tomcatzh/wallboard-rail-hooks/wiki/entities/mounting-rail.md

---
title: "Mounting Rail (wall panel insert strip)"
type: entity
status: active
sources:
  - raw/rail/hook-full-view.jpg
  - https://www.chinayoubang.com/productfamily/detail/195.html
updated: 2026-07-10
---

# Mounting Rail（墙板挂条）

## Summary（摘要）

EN: A champagne-gold aluminum strip inset horizontally into a seam of the white leather-textured wall paneling. Its front face carries fine horizontal ribs; along its top edge runs a continuous slot behind a front lip, into which claw-type hooks drop. It is existing infrastructure — the hook must adapt to it, not vice versa.
ZH: 一条水平嵌在白色皮纹墙板接缝中的香槟金色铝条。正面有细密水平棱纹；顶缘沿全长有一条位于前唇后方的连续槽，爪式挂钩由此扣入。它是既有设施 —— 是挂钩去适配它，而不是反过来。

## Product Identity（产品身份）

EN: The rail is the "parallel function strip" of Youbang wallboard's (友邦墙板) GuaGuaQiang (挂挂墙) Parallel series (平行系列) — official page: <https://www.chinayoubang.com/productfamily/detail/195.html>. Published spec: strip W×H×D = 3000×48×11 mm; material "native 6-series aluminum", anodized — consistent with the 6063-class assumption used in the strength review. Wallboard is Youbang "5K wood". Colors include 古铜黄 (antique bronze), matching our photos. The page does NOT publish slot/lip dimensions — the hook-side measurements in [rail-hook](rail-hook.md) remain the fit authority. Cite this section when publishing the project.
ZH: 挂条是友邦墙板「挂挂墙 · 平行系列」的"平行功能条" —— 官方页面：<https://www.chinayoubang.com/productfamily/detail/195.html>。公开规格：功能条 W×H×D = 3000×48×11 mm；材质"原生六系铝"、阳极氧化 —— 与强度审查中 6063 系的假设一致。墙板为友邦 5K 木。颜色含古铜黄，与我们的照片相符。页面**未**公布槽口/唇的尺寸 —— 配合仍以 [rail-hook](rail-hook.md) 中挂钩侧的实测为准。公开项目时引用本节说明来源。

## Observed Features（观察到的特征）

- EN: Ribbed front face; rib pitch well under 1 mm, visually matching the hook's serrated patch.
  ZH: 正面棱纹面；棱距远小于 1 mm，与挂钩的锯齿区在视觉上匹配。
- EN: A continuous dark slot line along the top edge where the hook's claw enters.
  ZH: 顶缘有一条连续深色缝线，挂钩的爪由此进入。
- EN: A smooth gold band above the ribbed strip (upper flange of the same profile, or a separate trim — undetermined).
  ZH: 棱纹条上方有一条光滑金色带（同一型材的上翻边，或独立饰条 —— 未确定）。
- EN: A 2026-07-10 caliper probe showed the earlier 1.6 mm lower-wallboard setback estimate was conservative, leading to otherwise-identical 2.0/2.5 mm half-width probes. The user selected 2.0 mm and promoted it into the production library. Treat 2.0 mm as the accepted accessory reach, not a direct measurement of the rail profile (the WeChat image remains in chat, not under `raw/`).
  ZH: 2026-07-10 的游标卡尺探测表明，此前下方墙板后退量 1.6 mm 的估计偏保守，因此制作了其余几何相同的 2.0/2.5 mm 半宽探针。用户最终选择 2.0 mm 并将其并入正式库。应把 2.0 mm 视为配件定案凸高，而不是轨道截面的直接实测值（WeChat 图片仍在聊天中，未存入 `raw/`）。
- EN: Implied clearances: the strip's bottom edge lies above the hook's wall pad (pad top ≈7–8.5 below the slot ceiling), and the panel above the strip is exposed at cap height (≈10.7–11.2 above the ceiling).
  ZH: 反推的空间关系：挂条下缘在挂钩抵墙凸台之上（凸台上缘约在槽顶下方 7–8.5）；挂条上方在顶帽高度（槽顶上方约 10.7–11.2）处露出墙板面。

## Interface Constraints Implied by the Hook（由挂钩尺寸反推的接口约束）

EN: The rail was not measured directly; these bounds follow from the hook's annotated dimensions (see [rail-hook](rail-hook.md)):
ZH: 挂条本身没有直接测量；以下边界由挂钩的标注尺寸反推（见 [rail-hook](rail-hook.md)）：

- EN: Top lip thickness < 2.75 mm (it must fit inside the claw slot).
  ZH: 上唇厚度 < 2.75 mm（要放进爪槽）。
- EN: Cavity behind the lip: ≥ ~2.4 mm front-to-back and ≥ ~6 mm deep (it must accept the claw finger).
  ZH: 上唇后方腔体：前后向 ≥ 约 2.4 mm、深度 ≥ 约 6 mm（要容纳爪指）。

## Superseded / Revised（已废弃 / 已修订）

- EN: "The strip front is uniformly ≈0.8 mm proud of the wall panel" — this 2026-07-09 inference came from the original hook's 0.8 mm top cap and back pad, not from a direct rail-to-panel measurement. The 2026-07-10 lower-panel observation is ≈1.6 mm, so upper and lower panel relationships must no longer be assumed identical.
  ZH: “挂条正面统一比墙板面凸出约 0.8 mm” —— 这个 2026-07-09 推论来自原钩顶部小帽与背面凸台均为 0.8 mm，并非轨道到墙板的直接测量。2026-07-10 对下方墙板的观察约为 1.6 mm，因此不能再假定轨道上下两侧的墙板空间关系完全相同。

## Open Questions（开放问题）

- EN: Exact rail profile (extrusion cross-section) and strip height are unknown — not required for replicating the hook, since the fit is already encoded in the hook's own dimensions.
  ZH: 挂条的精确型材截面与条高未知 —— 复刻挂钩并不需要它们，因为配合关系已经编码在挂钩自身尺寸里。
- EN: Whether the rail also has a bottom lip, and the exact lower-panel setback. The accessory geometry no longer depends on resolving these immediately because 2.0 mm has been selected, but a direct rail cross-section measurement would improve future variants.
  ZH: 挂条是否还有下唇，以及下方墙板的精确后退量。由于 2.0 mm 配件几何已经定案，当前不再依赖立即解决这些问题；但直接测得轨道截面仍可改进未来变体。
- EN: Interior headroom above the slot opening: my photo estimate put the opening at ≈4 mm, but the user (who has the rail in hand) judged a much larger reinforcement feasible — the hook's arc gusset now rises 7.2 above the ceiling inside the rail. Next test fit settles it: if the arc fouls the rail's interior or blocks tilt-in insertion, reduce `arm_gusset_r`.
  ZH: 槽口上方的内部净空：照片估计开口约 4 mm，但（手上有实物的）用户判断可以放大得多 —— 挂钩的圆弧加强现已在挂条内部升到槽顶上方 7.2。下一次试装可定案：若圆弧顶到挂条内部或妨碍斜插入，就调小 `arm_gusset_r`。
