tomcatzh/wallboard-rail-hooks/wiki/entities/rail-hook.md

---
title: "Rail Hook (replication target)"
type: entity
status: active
sources:
  - raw/rail/hook-mount-dimensions.jpg
  - raw/rail/hook-installed-on-rail.jpg
  - raw/rail/hook-full-view.jpg
updated: 2026-07-09
---

# Rail Hook（墙板轨道挂钩）

## Summary（摘要）

EN: A small J-shaped hanging hook in champagne-gold metal that clips tool-free onto a slatwall-style metal rail inset in wall paneling. It is the replication target of this project. The top "mounting claw" is the precision interface that engages the rail — its dimensions are annotated in the source photos and must be reproduced exactly. Per the user (2026-07-09), the overall height and the protruding J-hook are variable parts that may be adapted freely. See [hook-replication-requirements](../topics/hook-replication-requirements.md).
ZH: 一个香槟金色金属的小型 J 形挂钩，无需工具即可扣到嵌在墙板里的 slatwall（槽板）式金属挂条上。它是本项目的复刻对象。顶部的 mounting claw（安装爪）是与挂条配合的精密接口 —— 其尺寸在来源照片中有标注，必须精确复刻。用户已明确（2026-07-09）：总高与外伸的 J 钩是可变部分，可以自由调整。见 [hook-replication-requirements](../topics/hook-replication-requirements.md)。

## Construction（构造）

EN: The hook is almost certainly a slice cut from a long aluminum extrusion: the entire shape is a constant 2D profile swept along the hook's width, the front serration ridges run along that width axis, and the cut side faces show uniform machining marks. `hook-mount-dimensions.jpg` is literally the extrusion cross-section seen end-on. Consequence for replication: getting the 2D profile right (especially in the claw region) captures the entire fit; width is a separate single number.
ZH: 这个挂钩几乎可以肯定是从一根长 aluminum extrusion（铝挤出型材）上切下的一段：整个形状是一个恒定的 2D profile（二维截面）沿挂钩宽度方向扫掠而成，正面锯齿棱沿宽度方向延伸，切割侧面有均匀加工纹。`hook-mount-dimensions.jpg` 就是沿挤出轴方向看到的端面截面。对复刻的意义：把 2D 截面（尤其爪部区域）做准就抓住了全部配合关系；宽度只是另外一个独立数字。

EN: Descriptive coordinate convention for later reference (not a plan): the profile plane is the vertical plane perpendicular to the rail; +X points away from the wall (room side), +Y points up; the extrusion/width direction runs along the rail.
ZH: 为后续引用约定的描述性坐标（不是计划）：profile 平面为垂直于挂条的竖直平面；+X 指向远离墙面（房间一侧），+Y 向上；挤出/宽度方向沿挂条延伸。

## Profile, top to bottom（截面自上而下）

- EN: **Top cap** — a 0.5 mm tall cap at the plate top, thickened to 3.0 mm total by protruding 0.8 mm toward the wall (D15). It bears on the wall panel above the rail and stabilizes the hook against over-rotation. (The earlier "slanted top edge" reading is superseded — see below.)
  ZH: **顶部小帽** —— 主板顶部高 0.5 mm 的小帽，向墙面凸出 0.8 mm、总厚 3.0 mm（D15）。抵在挂条上方的墙板面上，防止挂钩过度转动、辅助受力。（早先“顶边斜切”的解读已废弃 —— 见下文。）
- EN: **Front face, serrated patch** — fine horizontal ridges (pitch well under 1 mm) covering roughly the top ~15 mm of the front face. When installed this patch overlaps the rail's ribbed face and visually blends the hook into the rail. The ridges face the room, so they are cosmetic, not a grip surface.
  ZH: **正面锯齿区** —— 细密水平棱纹（间距远小于 1 mm），覆盖正面顶部约 15 mm。安装后这块区域正好叠在挂条的棱纹面上，使挂钩在视觉上融入挂条。棱纹朝向房间一侧，是装饰性的，不是摩擦面。
- EN: **Mounting claw (back side)** — below the plate top, a bridge arm projects rearward (toward the wall) from the plate, then turns down into a rear finger, forming a downward-opening claw. The gap between finger and plate is the slot that swallows the rail's top lip. Front-to-back order when installed: plate (room side) → slot (rail lip sits here) → finger (wall side). Outer corners are slightly rounded; the finger tip is a slanted point (user-confirmed 2026-07-09): lowest at the outer/wall face, its bottom rising ≈1.5 mm toward the inner face — an insertion ramp that rides over the lip during tilt-in.
  ZH: **安装爪（背面）** —— 在主板顶部下方，一条 bridge arm（顶桥）从主板向后（朝墙）伸出，再向下折成后爪指，构成开口朝下的爪。爪指与主板之间的缝隙就是吞住挂条上唇的槽。安装后从前到后的顺序：主板（房间侧）→ 槽（挂条上唇在此）→ 爪指（墙侧）。外侧转角略有圆角；爪指末端是斜尖（用户 2026-07-09 确认）：最低点在外侧/墙侧，底面向内侧斜升约 1.5 mm —— 翻入轨道时骑过上唇的导向斜面。
- EN: **Back wall pad** — below the rail zone the back face bulges 0.8 mm TOWARD the wall (total 3.0 mm thick, D13) and runs down into the J. It braces against the wall panel and carries the horizontal reaction H — the original's built-in answer to the tipping moment. Together with the cap it implies the panel surface sits ≈0.8 mm behind the rail face.
  ZH: **背面抵墙凸台** —— 挂条区以下，背面向墙面方向凸出 0.8 mm（总厚 3.0 mm，D13），向下延伸并入 J 钩。它抵住墙板、承担水平反力 H —— 是原件对倾覆力矩的自带解决方案。结合小帽可推出：墙板面比挂条正面靠后约 0.8 mm。
- EN: **J-hook** — the shank sweeps into a J curve opening up-and-away from the wall; the section appears to thicken gradually toward the tip end of the curve. A small V-notch is visible on the inner face right at the tip in the bare-hook photo (possibly a retention nib for loops/strings, possibly a cutting artifact — unconfirmed).
  ZH: **J 钩** —— 杆身向下弯成 J 形曲线，开口朝上并远离墙面；截面似乎向钩尖一端逐渐加厚。裸钩照片中钩尖内侧面可见一个小 V 形缺口（可能是防止挂绳滑落的小卡口，也可能是切割痕迹 —— 未确认）。

## Dimensions（尺寸）

EN: D1–D3 are the three annotations written on `hook-mount-dimensions.jpg` and are the authoritative numbers. D4 is derived from them. All others are photo-scale estimates: calibrated at ≈23 px/mm on the bare-hook profile photo using D1 as scale; the claw's total depth then measures ≈7.4 mm, matching D3 = 7.35 mm, which validates the scale.
ZH: D1–D3 是写在 `hook-mount-dimensions.jpg` 上的三个标注，是权威数字。D4 由它们推导。其余均为照片比例估计：以 D1 为尺度在裸钩侧面照上标定 ≈23 px/mm；用该尺度量得爪部总深 ≈7.4 mm，与 D3 = 7.35 mm 吻合，验证了该比例。

| # | Feature（部位） | Value | Basis（依据） | Confidence |
|---|---|---|---|---|
| D1 | Rear finger thickness, wall-normal（后爪指厚度，垂直墙面方向） | 2.40 mm | annotated（照片标注） | high |
| D2 | Claw slot gap, finger↔plate（爪槽宽，容纳挂条上唇） | 2.75 mm | annotated | high — user-confirmed（用户已确认） |
| D3 | Mounting-head total depth, serrated front face→finger back face（安装头总深：锯齿正面→爪指背面） | 7.35 mm | annotated | high |
| D4 | Plate thickness at claw level（主板在爪部高度的厚度） | ≈2.20 mm | derived: D3−D2−D1 | medium |
| D5 | Bridge-arm vertical thickness（顶桥竖直厚度） | ≈2.2 mm | photo-scale estimate | low — measure |
| D6 | Finger vertical length / slot depth（爪指竖直长度 / 槽深） | 6.75 mm (claw total arm+finger = 9.0 measured) | user caliper 2026-07-09 | high — measured（已实测） |
| D7 | Plate extension above bridge-arm top（主板高出顶桥的高度） | 8.8 mm (build 9.0) | user caliper 2026-07-09 | high — measured（已实测） |
| D8 | Serrated patch height（正面锯齿区高度） | ≈15 mm | photo-scale estimate | low |
| D9 | Overall hook height（挂钩总高） | ≈40 mm | photo-scale estimate | variable by design（设计可变） |
| D10 | Hook width along rail（挂钩宽度，沿挂条/挤出方向） | 11.9 mm | user caliper 2026-07-09 | high — measured; still design-variable（已实测；仍可自由改） |
| D11 | J-hook inner radius（J 钩内半径） | ≈5–6 mm | photo-scale estimate | variable by design（设计可变） |
| D12 | J-hook wall thickness（J 钩壁厚） | ≈2.8–4 mm (thickens toward tip end) | photo-scale estimate | variable by design（设计可变） |
| D13 | Back wall pad（背面抵墙凸台） | total 3.0 thick = 0.8 wall-ward of plate back; top edge ≈7–8.5 below ceiling, runs into the J（总厚 3.0 = 向墙凸 0.8；上缘在槽顶下方≈7–8.5，向下并入 J） | user statement + photos 2026-07-09 | high (thickness) / low (top edge) |
| D14 | Serration pitch（锯齿间距） | ≈0.5–0.8 mm | photo-scale estimate | very low |
| D15 | Top cap（顶部小帽） | 0.5 tall × 3.0 total thick, 0.8 wall-ward（高 0.5 × 总厚 3.0，向墙凸 0.8） | user caliper 2026-07-09 | high — measured |
| D16 | Finger tip taper（爪尖斜面高度） | ≈1.5, point at the outer face（尖在外侧/墙侧） | photo estimate; direction user-confirmed | medium |

EN: Basis legend — annotated = written on the photo; derived = computed from annotated values; estimate = pixel-scale reading. Everything at low/very-low confidence must be caliper-measured before modeling; see the wishlist in [hook-replication-requirements](../topics/hook-replication-requirements.md).
ZH: 依据说明 —— annotated = 照片上的标注；derived = 由标注值推导；estimate = 像素比例读数。所有 low / very low 置信度的尺寸在建模前必须用卡尺实测，见 [hook-replication-requirements](../topics/hook-replication-requirements.md) 的待测清单。

## Annotation Interpretation（标注解读）

EN: The three annotations are tick-mark pairs drawn on the cross-section photo; the mapping below was determined from tick positions relative to the profile features.
ZH: 三个标注是画在截面照片上的成对刻度线；下面的对应关系由刻度线相对截面特征的位置判定。

- EN: **2.4 mm** — the tick pair flanks the rear finger, label below it → rear finger thickness (D1). High confidence.
  ZH: **2.4 mm** —— 刻度线夹住后爪指，标签在其下方 → 后爪指厚度（D1）。高置信度。
- EN: **2.75 mm** — the tick pair is drawn above the bridge arm but horizontally aligns with the slot walls (finger inner face / plate back face) → slot gap (D2). High-medium confidence.
  ZH: **2.75 mm** —— 刻度线画在顶桥上方，但水平位置对齐槽的两壁（爪指内侧面 / 主板背面）→ 槽宽（D2）。中高置信度。
- EN: **7.35 mm** — the tick pair flanks the whole head, from finger back face to plate front (serrated) face → total mounting-head depth (D3). High confidence.
  ZH: **7.35 mm** —— 刻度线夹住整个安装头，从爪指背面到主板正面（锯齿面）→ 安装头总深（D3）。高置信度。
- EN: Caveat: in both photos the slot *looks* narrower than the finger, yet the annotations say slot 2.75 > finger 2.4. Shadow inside the slot plus perspective (the finger sits closer to the camera) explains this, and the numbers are self-consistent (D4 ≈ 2.2 mm plate ≈ bridge-arm thickness ≈ a uniform extrusion wall), but user confirmation is welcome.
  ZH: 注意：两张照片里槽*看起来*都比爪指窄，而标注却是槽 2.75 > 爪指 2.4。槽内阴影加上透视（爪指更靠近相机）可以解释，且数字自洽（D4 ≈ 2.2 mm 主板厚 ≈ 顶桥厚 ≈ 均匀挤出壁厚），但欢迎用户确认。
- EN: Confirmed: on 2026-07-09 the user reviewed side-view sketches drawn from this interpretation (including the claw-over-lip mounting model) and confirmed they are correct. The mapping above is settled.
  ZH: 已确认：2026-07-09 用户审阅了按此解读绘制的侧视图草图（含爪扣上唇的安装模型），确认无误。上述对应关系定案。

## Mounting Interaction（安装配合）

EN: To install, the claw drops over the rail's top edge from the front: the rail's top lip enters the 2.75 mm slot, the 2.4 mm finger hides behind the lip inside the rail cavity, and the plate's smooth back face rests on the lip's front face. Load on the J-hook torques the hook so the lower shank presses toward the wall — self-locking, no fasteners. The serrated patch overlaps the rail's ribbed face for visual continuity. See [mounting-rail](mounting-rail.md).
ZH: 安装时，安装爪从前方扣到挂条顶缘上：挂条上唇进入 2.75 mm 的槽，2.4 mm 的爪指藏进上唇后方的挂条腔体，主板光滑的背面贴在上唇正面。J 钩受载产生的力矩使下段杆身压向墙面 —— 自锁，无需紧固件。锯齿区叠在挂条棱纹面上，保持视觉连续。见 [mounting-rail](mounting-rail.md)。

## Evidence（证据）

- EN: `raw/rail/hook-mount-dimensions.jpg` — end-on cross-section of the mounting head with the three dimension annotations; serration teeth visible on the front edge.
  ZH: `raw/rail/hook-mount-dimensions.jpg` —— 安装头的端面截面，带三个尺寸标注；正面边缘可见锯齿。
- EN: `raw/rail/hook-installed-on-rail.jpg` — despite its filename, shows the bare hook's full side profile on a plain background; source of the photo-scale estimates.
  ZH: `raw/rail/hook-installed-on-rail.jpg` —— 与文件名相反，实际是纯色背景上裸钩的完整侧面轮廓；照片比例估计的来源。
- EN: `raw/rail/hook-full-view.jpg` — despite its filename, shows the hook installed on the gold rail in the wall paneling; source for the mounting interaction and rib blending.
  ZH: `raw/rail/hook-full-view.jpg` —— 与文件名相反，实际是挂钩安装在墙板金色挂条上的照片；安装配合与棱纹融合观察的来源。
- EN: 2026-07-09 chat photos — a v3 print seats correctly on the real rail (claw over lip, cap and pad engaged): the mount interface is physically validated.
  ZH: 2026-07-09 对话照片 —— v3 打印件在真实挂条上正确就位（爪扣唇、帽与凸台到位）：安装接口已实物验证。

## Superseded（已废弃的解读）

- EN: "Slanted top edge (front high, sloping to the wall side)" — superseded 2026-07-09 by the user's close-up photos and calipers: the feature is the 0.5×3.0 top cap (D15).
  ZH: “顶边斜切（前高后低）” —— 2026-07-09 被用户微距照片与卡尺推翻：该特征实为 0.5×3.0 的顶部小帽（D15）。
- EN: "Back-face step toward the room (shank thinner below)" — superseded: the feature is the 0.8 mm wall-ward pad (D13). hook.scad v1/v2 modeled the wrong direction; corrected in v3.
  ZH: “背面向房间收薄的台阶” —— 已废弃：该特征实为向墙凸 0.8 mm 的抵墙凸台（D13）。hook.scad v1/v2 方向建反；v3 已纠正。
- EN: "D7 ≈ 6.5–7 mm" — superseded by caliper 8.8 mm. Root cause: photo verticals are foreshortened ≈25% (perspective); remaining photo-derived vertical estimates (D5, D6, D8, D9) should be read ≈25% larger until measured.
  ZH: “D7 ≈ 6.5–7 mm” —— 被卡尺实测 8.8 mm 取代。根因：照片竖直方向被透视压缩约 25%；其余照片竖直估计（D5、D6、D8、D9）在实测前都应按放大约 25% 理解。

## Open Questions（开放问题）

- EN: D6 settled: claw total (arm+finger) caliper-measured ≈9.0 → finger 6.75 with the arm at 2.2. D5 (arm) itself is still a photo estimate, but the user's 6.75 split implies arm ≈2.2–2.25, so the earlier ≈2.7 suspicion is retracted; the authoritative number is the 9.0 total.
  ZH: D6 定案：爪部总高（顶桥+爪指）卡尺实测 ≈9.0 → 顶桥按 2.2 时爪指为 6.75。D5（顶桥）本身仍是照片估计，但用户给出的 6.75 拆分意味着顶桥 ≈2.2–2.25，此前 ≈2.7 的猜测撤回；权威数字是总高 9.0。
- EN: Wall-pad top edge height (D13) — must clear the rail strip's bottom edge; the model defaults to 8.0 below the ceiling. Confirm at test fit.
  ZH: 抵墙凸台上缘高度（D13）—— 必须让开挂条下缘；模型默认取槽顶下方 8.0。试装确认。
- EN: Tip V-notch and serration details (D8, D14) sit in the variable body — replicate loosely or drop.
  ZH: 钩尖 V 缺口与锯齿细节（D8、D14）属于可变部分 —— 可宽松复刻或省略。
