tomcatzh/wallboard-rail-hooks/raw/accessories/frame-ribba22/existing-flat-hook.jpg

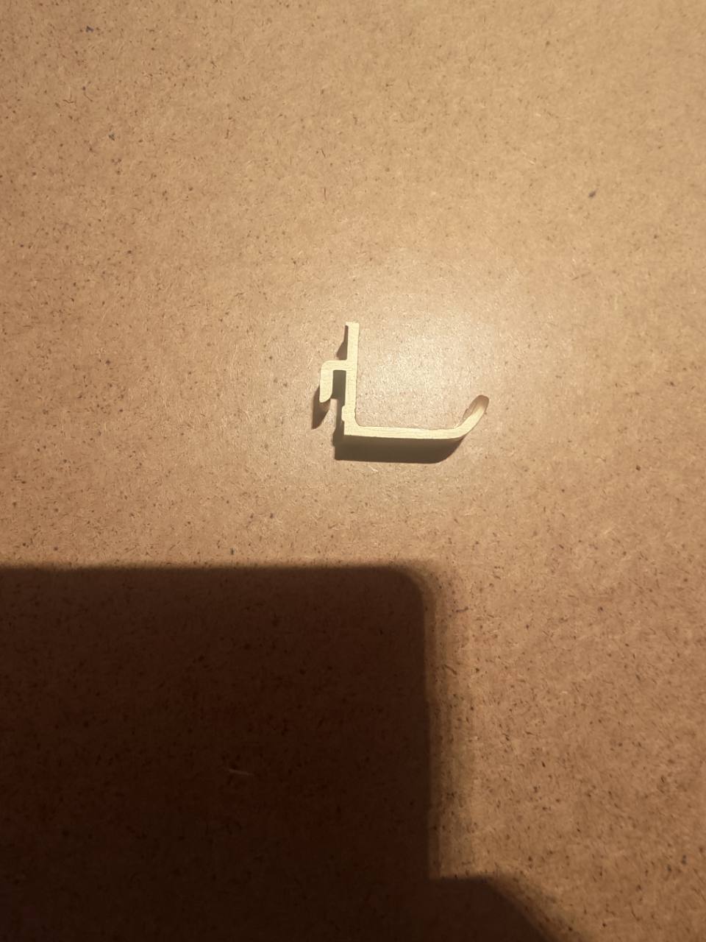
raw/accessories/frame-ribba22/existing-flat-hook.jpg
