tomcatzh/wallboard-rail-hooks/raw/accessories/frame-ribba22/recessed-back.jpg

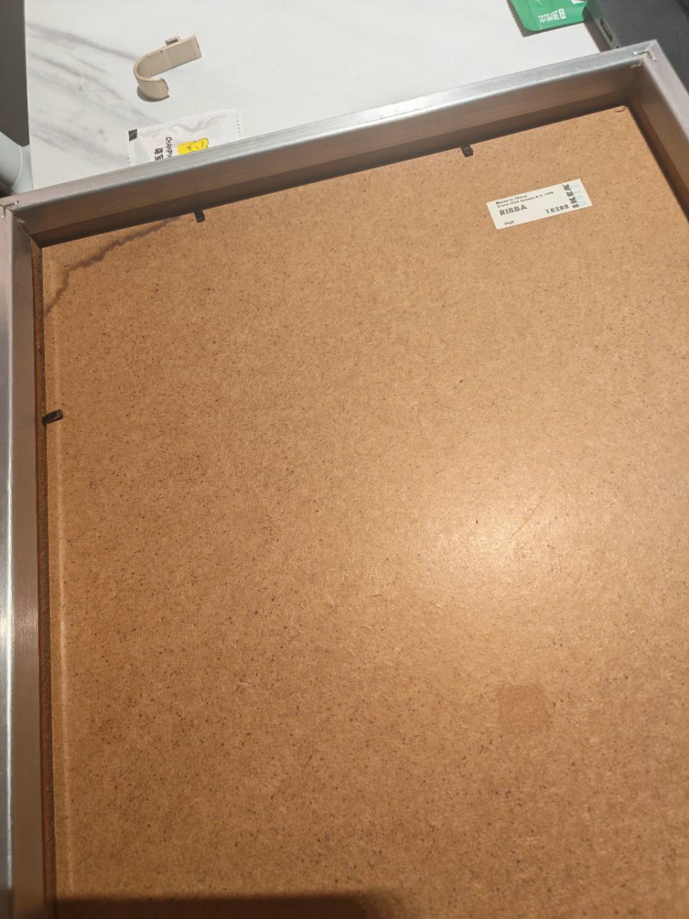
raw/accessories/frame-ribba22/recessed-back.jpg
