tomcatzh/wallboard-rail-hooks/raw/accessories/frame-ribba22/ribba-label.jpg

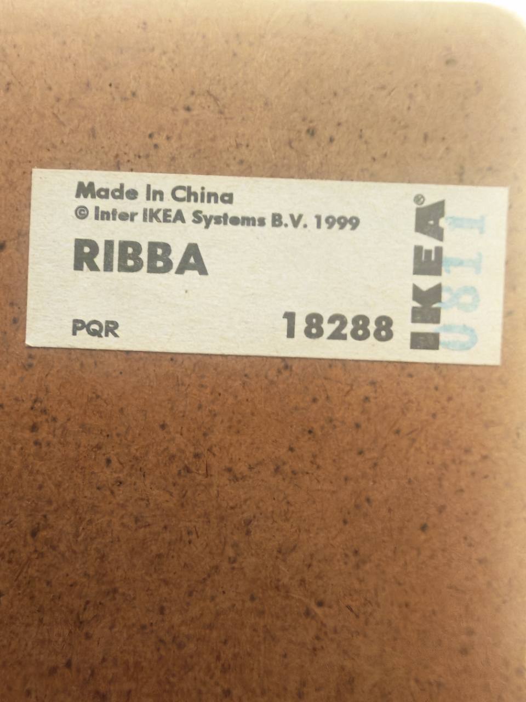
raw/accessories/frame-ribba22/ribba-label.jpg
