tomcatzh/wallboard-rail-hooks/raw/accessories/hook-keyhole9/reference.jpg

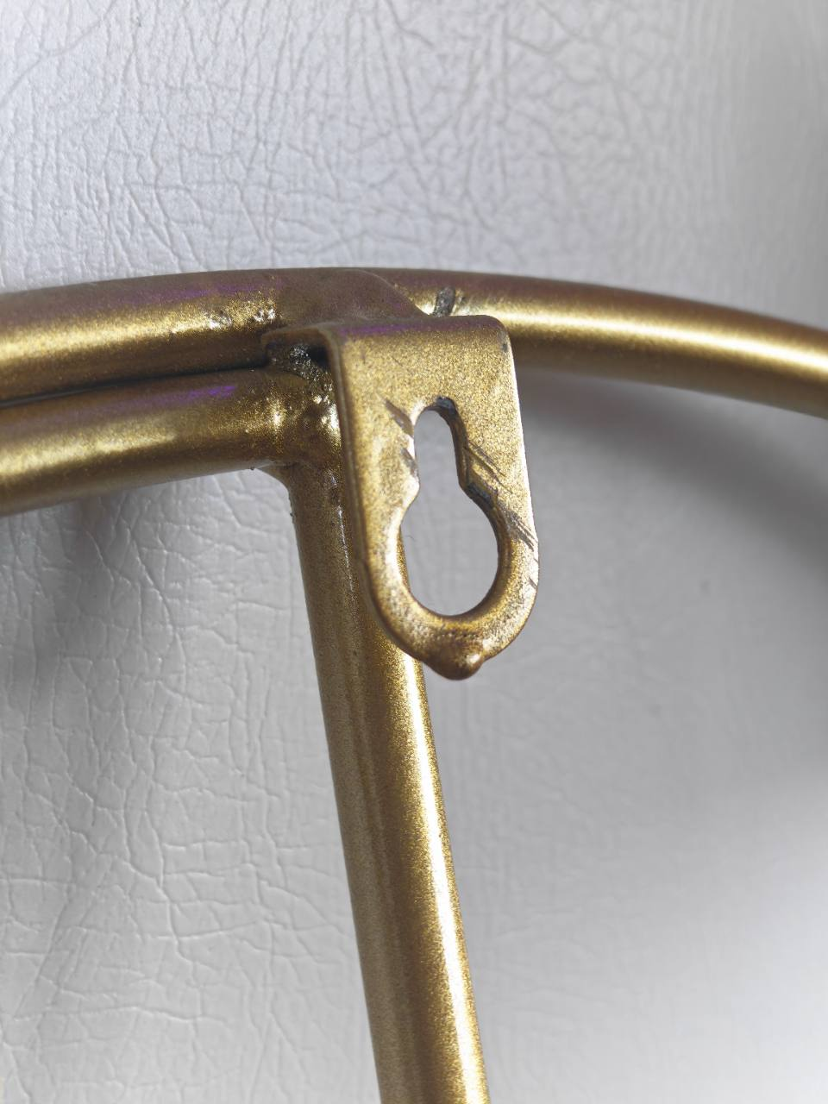
raw/accessories/hook-keyhole9/reference.jpg
