tomcatzh/wallboard-rail-hooks/raw/rail/hook-mount-dimensions.jpg

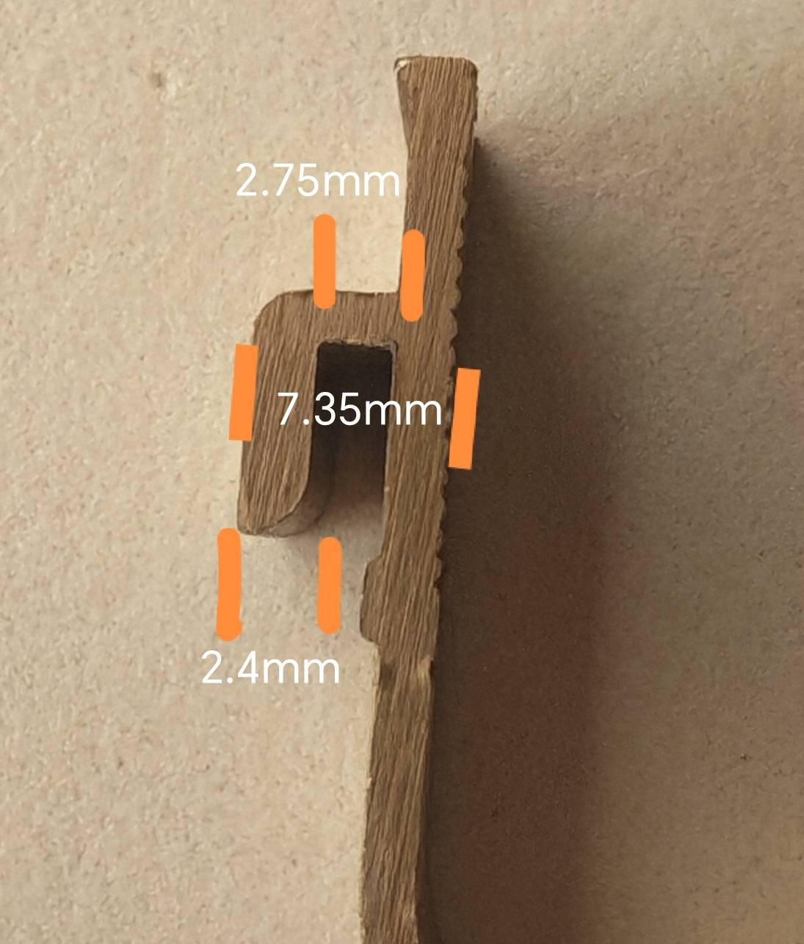
raw/rail/hook-mount-dimensions.jpg
