tomcatzh/wallboard-rail-hooks/raw/rail/hook-installed-on-rail.jpg

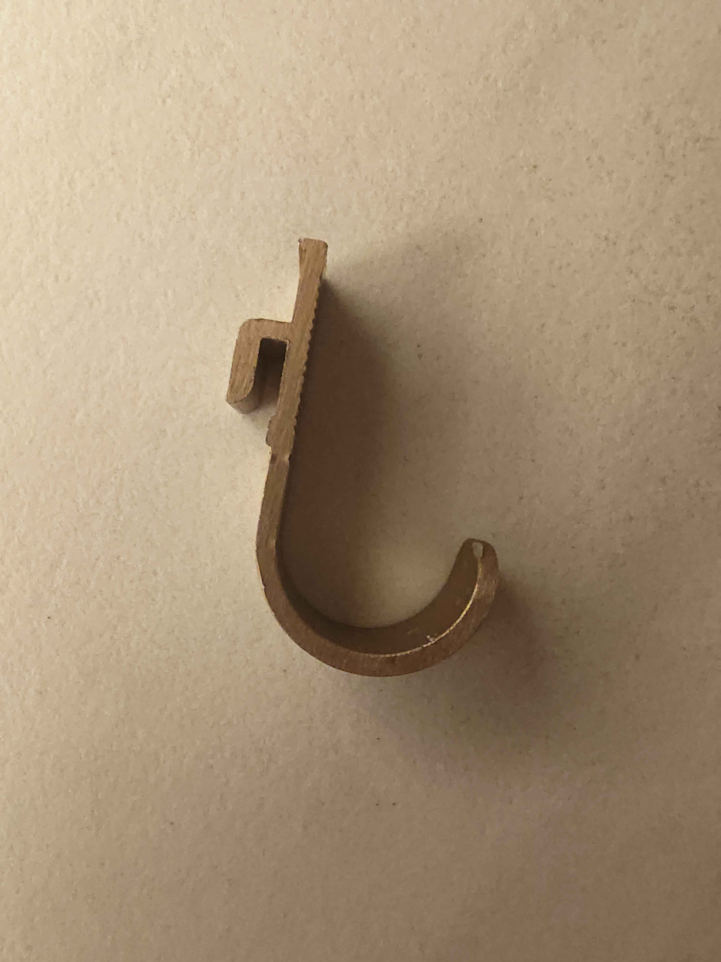
raw/rail/hook-installed-on-rail.jpg
